Brink2Three/MTA-LED-Map-Raspi/maps/Point maps/85LEDS - Bottom half LED count.png

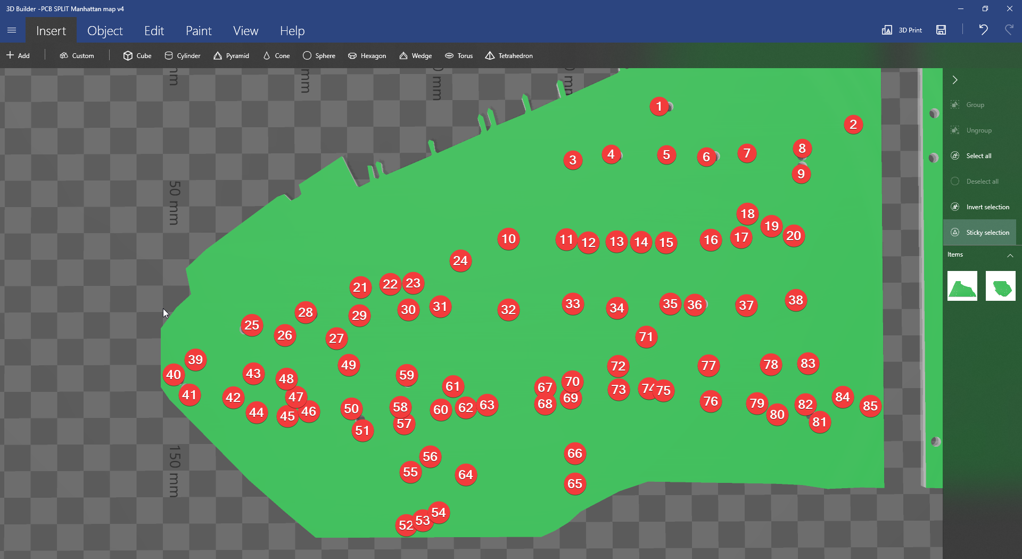
maps/Point maps/85LEDS - Bottom half LED count.png
