Brink2Three/MTA-LED-Map-Raspi/maps/Point maps/Top of manhattan/Top-Manhattan-dotsv2.png

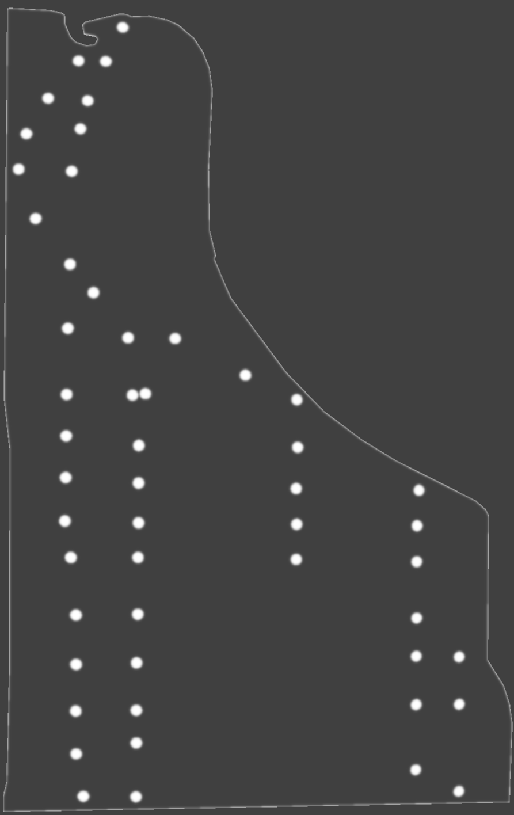
maps/Point maps/Top of manhattan/Top-Manhattan-dotsv2.png
