Brink2Three/MTA-LED-Map-Raspi/maps/Point maps/Manhattan map part 1 v2.stl

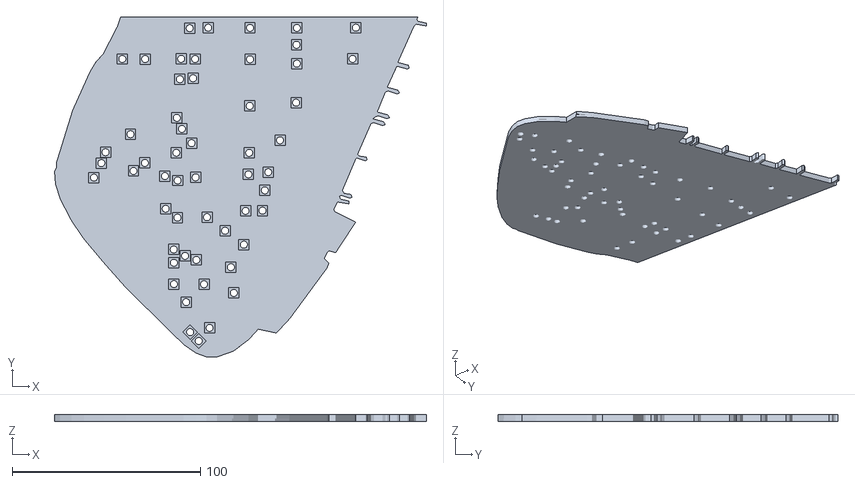
[picture p24: CAD file, 2023-12-12]
maps/Point maps/Manhattan map part 1 v2.stl
197.6 x 180.5 x 3.59
