Brink2Three/MTA-LED-Map-Raspi/maps/Point maps/v4Manhattan TOP.stl

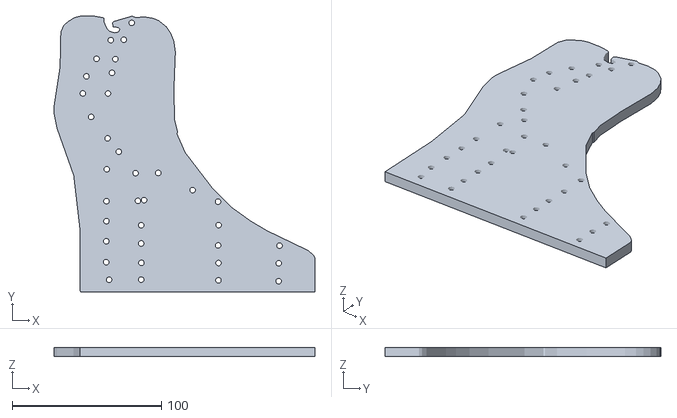
[picture p25: CAD file, 2023-12-12]
maps/Point maps/v4Manhattan TOP.stl
174.8 x 184.6 x 6.35
